r00kie/arduhog/src/arduhog/EventFunctions.h

void ic0btn0pressed() {
  UsbKeyboard.sendKeyStroke(KEY_0, MOD_SHIFT_LEFT | MOD_ALT_LEFT | MOD_CONTROL_LEFT | MOD_ALT_RIGHT | MOD_CONTROL_RIGHT);   
}

void ic0btn0released() {
  UsbKeyboard.sendKeyStroke(KEY_0,                  MOD_ALT_LEFT | MOD_CONTROL_LEFT | MOD_ALT_RIGHT | MOD_CONTROL_RIGHT);     
}

void ic0btn1pressed() {  
  UsbKeyboard.sendKeyStroke(KEY_1, MOD_SHIFT_LEFT | MOD_ALT_LEFT | MOD_CONTROL_LEFT | MOD_ALT_RIGHT | MOD_CONTROL_RIGHT);   
}

void ic0btn1released() {
  UsbKeyboard.sendKeyStroke(KEY_2,                  MOD_ALT_LEFT | MOD_CONTROL_LEFT | MOD_ALT_RIGHT | MOD_CONTROL_RIGHT);   
}

void ic0btn2pressed() {  
  UsbKeyboard.sendKeyStroke(KEY_2, MOD_SHIFT_LEFT | MOD_ALT_LEFT | MOD_CONTROL_LEFT | MOD_ALT_RIGHT | MOD_CONTROL_RIGHT);   
}

void ic0btn2released() {  
  UsbKeyboard.sendKeyStroke(KEY_2,                  MOD_ALT_LEFT | MOD_CONTROL_LEFT | MOD_ALT_RIGHT | MOD_CONTROL_RIGHT);   
}

void ic0btn3pressed() {  
  UsbKeyboard.sendKeyStroke(KEY_3, MOD_SHIFT_LEFT | MOD_ALT_LEFT | MOD_CONTROL_LEFT | MOD_ALT_RIGHT | MOD_CONTROL_RIGHT); 
}

void ic0btn3released() {  
  UsbKeyboard.sendKeyStroke(KEY_3, MOD_SHIFT_LEFT | MOD_ALT_LEFT | MOD_CONTROL_LEFT | MOD_ALT_RIGHT | MOD_CONTROL_RIGHT); 
}

void ic0btn4pressed() {  
  UsbKeyboard.sendKeyStroke(KEY_4, MOD_SHIFT_LEFT | MOD_ALT_LEFT | MOD_CONTROL_LEFT | MOD_ALT_RIGHT | MOD_CONTROL_RIGHT);  
}

void ic0btn4released() {  
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
}

void ic6btn11pressed() {
}

void ic6btn11released() {
}

void ic6btn12pressed() {
}

void ic6btn12released() {
}

void ic6btn13pressed() {
}

void ic6btn13released() {
}

void ic6btn14pressed() {
}

void ic6btn14released() {
}

void ic6btn15pressed() {
}

void ic6btn15released() {
}

void (*pressed_event[])() = { ic0btn0pressed, ic0btn1pressed, ic0btn2pressed, ic0btn3pressed, ic0btn4pressed, ic0btn5pressed, ic0btn6pressed, ic0btn7pressed, ic0btn8pressed, ic0btn9pressed, ic0btn10pressed, ic0btn11pressed, ic0btn12pressed, ic0btn13pressed, ic0btn14pressed, ic0btn15pressed, ic1btn0pressed, ic1btn1pressed, ic1btn2pressed, ic1btn3pressed, ic1btn4pressed, ic1btn5pressed, ic1btn6pressed, ic1btn7pressed, ic1btn8pressed, ic1btn9pressed, ic1btn10pressed, ic1btn11pressed, ic1btn12pressed, ic1btn13pressed, ic1btn14pressed, ic1btn15pressed, ic2btn0pressed, ic2btn1pressed, ic2btn2pressed, ic2btn3pressed, ic2btn4pressed, ic2btn5pressed, ic2btn6pressed, ic2btn7pressed, ic2btn8pressed, ic2btn9pressed, ic2btn10pressed, ic2btn11pressed, ic2btn12pressed, ic2btn13pressed, ic2btn14pressed, ic2btn15pressed, ic3btn0pressed, ic3btn1pressed, ic3btn2pressed, ic3btn3pressed, ic3btn4pressed, ic3btn5pressed, ic3btn6pressed, ic3btn7pressed, ic3btn8pressed, ic3btn9pressed, ic3btn10pressed, ic3btn11pressed, ic3btn12pressed, ic3btn13pressed, ic3btn14pressed, ic3btn15pressed, ic4btn0pressed, ic4btn1pressed, ic4btn2pressed, ic4btn3pressed, ic4btn4pressed, ic4btn5pressed, ic4btn6pressed, ic4btn7pressed, ic4btn8pressed, ic4btn9pressed, ic4btn10pressed, ic4btn11pressed, ic4btn12pressed, ic4btn13pressed, ic4btn14pressed, ic4btn15pressed, ic5btn0pressed, ic5btn1pressed, ic5btn2pressed, ic5btn3pressed, ic5btn4pressed, ic5btn5pressed, ic5btn6pressed, ic5btn7pressed, ic5btn8pressed, ic5btn9pressed, ic5btn10pressed, ic5btn11pressed, ic5btn12pressed, ic5btn13pressed, ic5btn14pressed, ic5btn15pressed, ic6btn0pressed, ic6btn1pressed, ic6btn2pressed, ic6btn3pressed, ic6btn4pressed, ic6btn5pressed, ic6btn6pressed, ic6btn7pressed, ic6btn8pressed, ic6btn9pressed, ic6btn10pressed, ic6btn11pressed, ic6btn12pressed, ic6btn13pressed, ic6btn14pressed, ic6btn15pressed };
void (*released_event[])() = { ic0btn0released, ic0btn1released, ic0btn2released, ic0btn3released, ic0btn4released, ic0btn5released, ic0btn6released, ic0btn7released, ic0btn8released, ic0btn9released, ic0btn10released, ic0btn11released, ic0btn12released, ic0btn13released, ic0btn14released, ic0btn15released, ic1btn0released, ic1btn1released, ic1btn2released, ic1btn3released, ic1btn4released, ic1btn5released, ic1btn6released, ic1btn7released, ic1btn8released, ic1btn9released, ic1btn10released, ic1btn11released, ic1btn12released, ic1btn13released, ic1btn14released, ic1btn15released, ic2btn0released, ic2btn1released, ic2btn2released, ic2btn3released, ic2btn4released, ic2btn5released, ic2btn6released, ic2btn7released, ic2btn8released, ic2btn9released, ic2btn10released, ic2btn11released, ic2btn12released, ic2btn13released, ic2btn14released, ic2btn15released, ic3btn0released, ic3btn1released, ic3btn2released, ic3btn3released, ic3btn4released, ic3btn5released, ic3btn6released, ic3btn7released, ic3btn8released, ic3btn9released, ic3btn10released, ic3btn11released, ic3btn12released, ic3btn13released, ic3btn14released, ic3btn15released, ic4btn0released, ic4btn1released, ic4btn2released, ic4btn3released, ic4btn4released, ic4btn5released, ic4btn6released, ic4btn7released, ic4btn8released, ic4btn9released, ic4btn10released, ic4btn11released, ic4btn12released, ic4btn13released, ic4btn14released, ic4btn15released, ic5btn0released, ic5btn1released, ic5btn2released, ic5btn3released, ic5btn4released, ic5btn5released, ic5btn6released, ic5btn7released, ic5btn8released, ic5btn9released, ic5btn10released, ic5btn11released, ic5btn12released, ic5btn13released, ic5btn14released, ic5btn15released, ic6btn0released, ic6btn1released, ic6btn2released, ic6btn3released, ic6btn4released, ic6btn5released, ic6btn6released, ic6btn7released, ic6btn8released, ic6btn9released, ic6btn10released, ic6btn11released, ic6btn12released, ic6btn13released, ic6btn14released, ic6btn15released };
